andreeaszabo10/E-book-Reader/Images/bottom.png

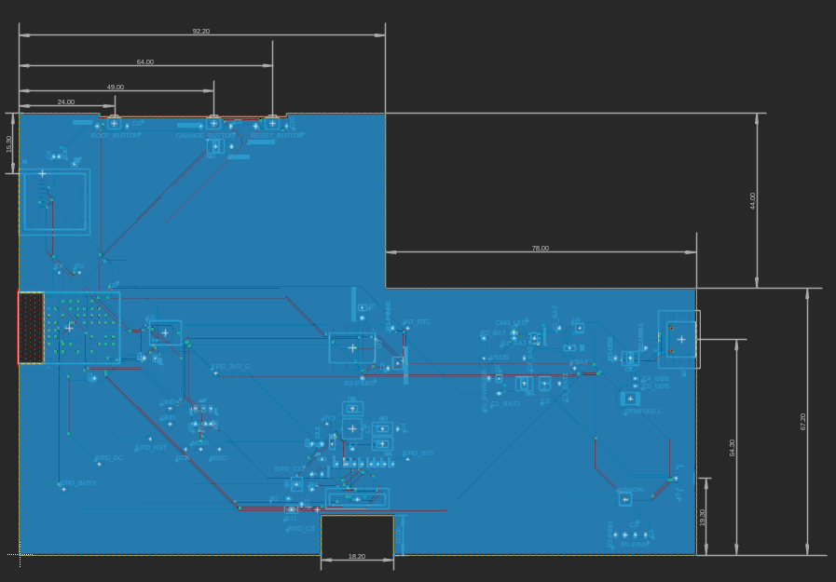
Images/bottom.png
